ymkn/henge40/image/temp.jpg

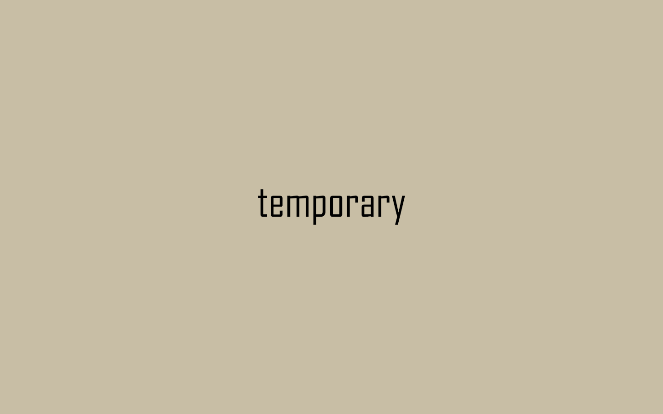
image/temp.jpg
