ymkn/henge40/KiCAD/PCB/production/Henge40_PCB_v1.0/Henge40_PCB.png

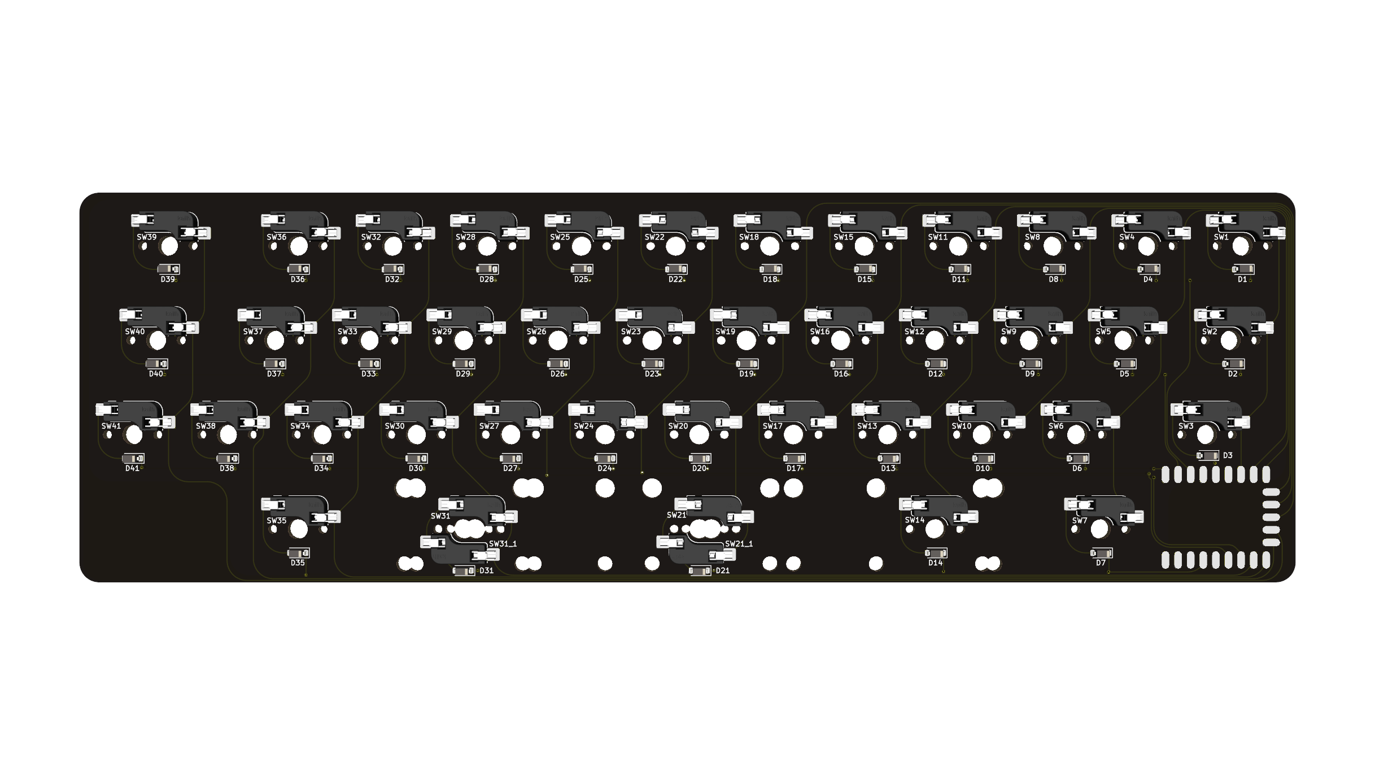
KiCAD/PCB/production/Henge40_PCB_v1.0/Henge40_PCB.png
